iosonofabio/fabiTEM/pcb/3D/SW_SKHLLC.step

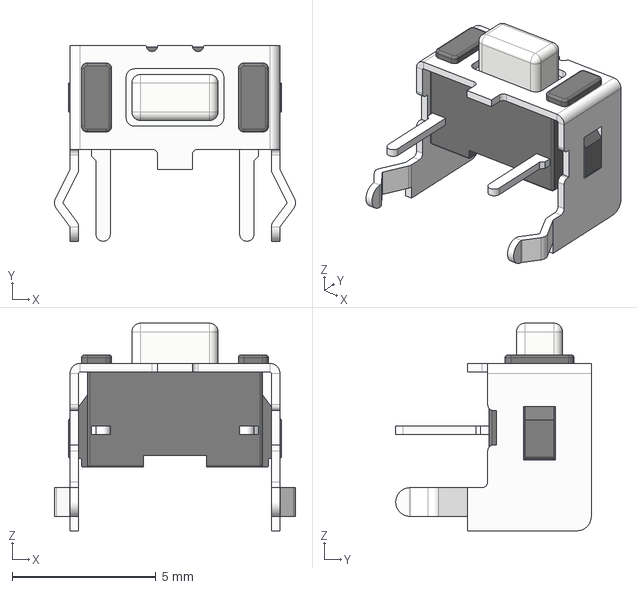
[picture p17: CAD file, 2024-05-21]
pcb/3D/SW_SKHLLC.step
8.38 x 6.80 x 7.22 mm
