iosonofabio/fabiTEM/pcb/3D/D_SOD-123.step

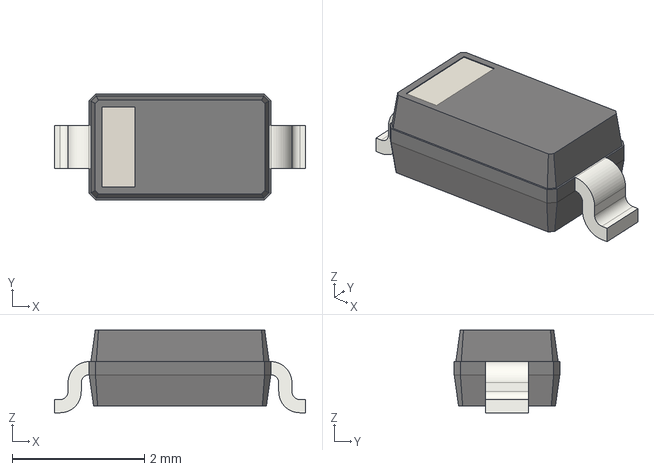
[picture p18: CAD file, 2024-05-21]
pcb/3D/D_SOD-123.step
3.80 x 1.60 x 1.25 mm
