iosonofabio/fabiTEM/pcb/3D/Kailh_socket_PG1350_optional.STEP

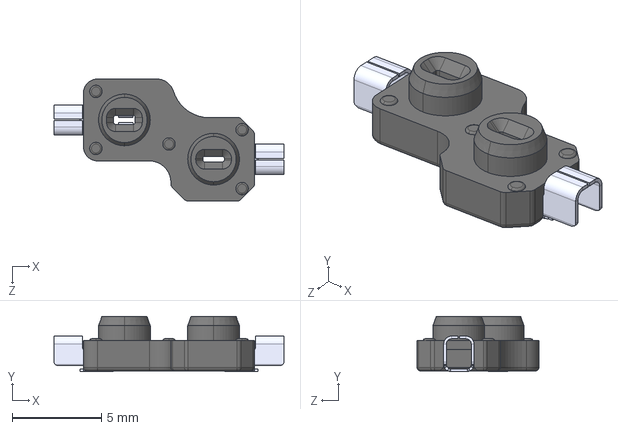
[picture p19: CAD file, 2024-05-21]
pcb/3D/Kailh_socket_PG1350_optional.STEP
12.9 x 3.09 x 6.85 mm
pin x 2
socket
