iosonofabio/fabiTEM/pcb/3D/Kailh_switch_PG1350_optional.step

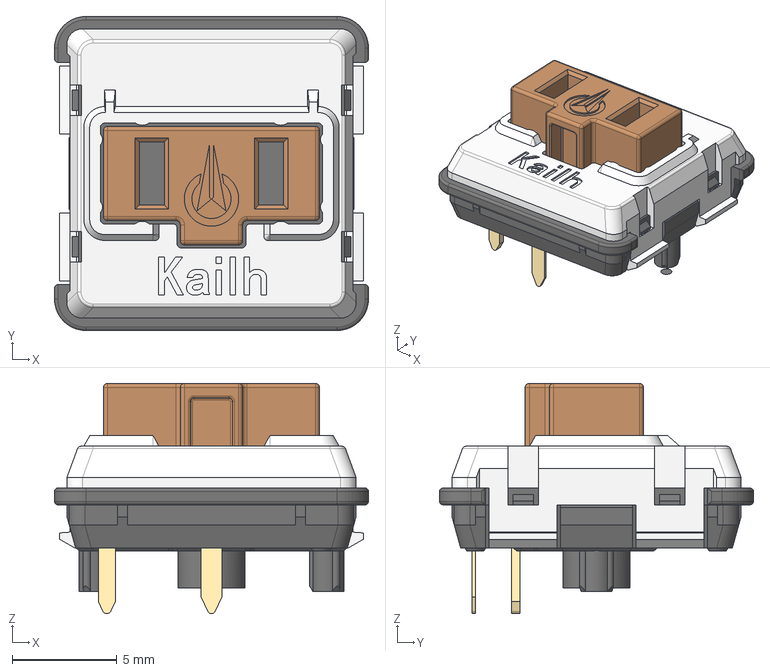
[picture p20: CAD file, 2024-05-21]
pcb/3D/Kailh_switch_PG1350_optional.step
15.0 x 15.0 x 11.0 mm
