iosonofabio/fabiTEM/pcb/3D/MSK12C02.STEP

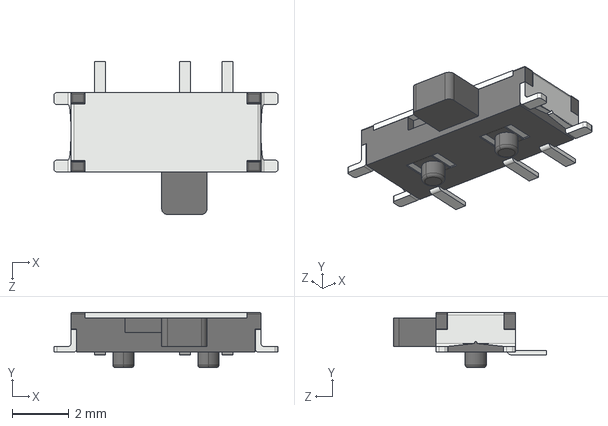
[picture p21: CAD file, 2024-05-21]
pcb/3D/MSK12C02.STEP
7.90 x 1.95 x 5.39 mm
