iosonofabio/fabiTEM/pcb/fabiTEM.kicad_sch

## KiCad design pcb/fabiTEM.kicad_sch (2025-03-23)

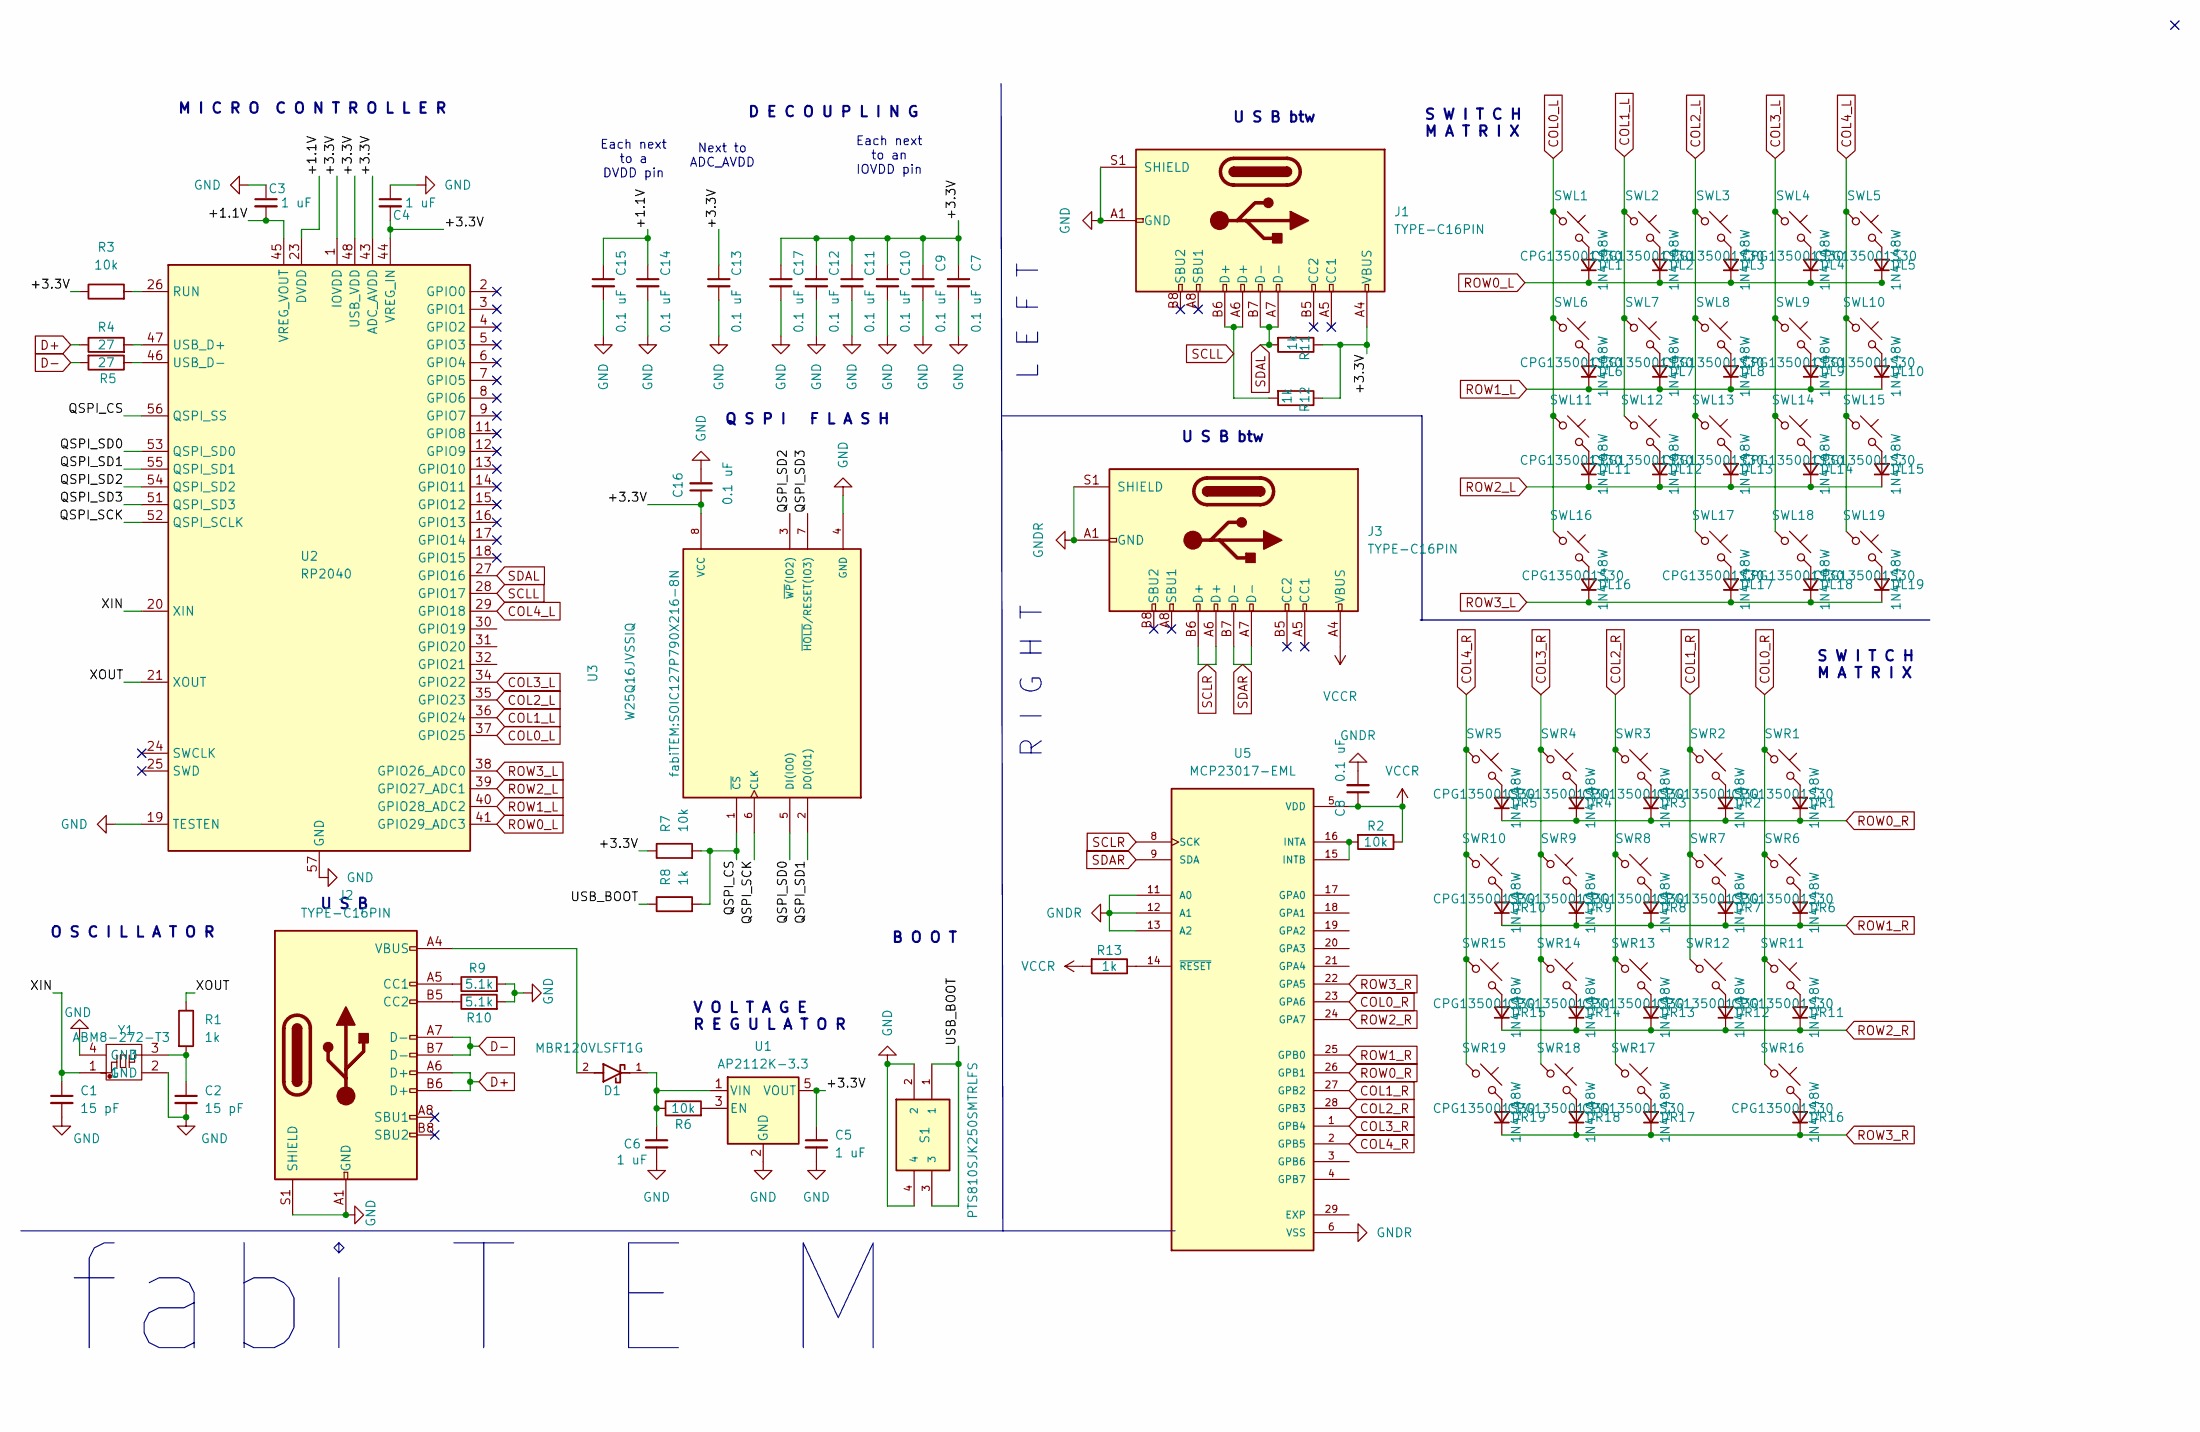
[picture p23: schematic fabiTEM.kicad_sch]

Parts:
C1, C2: 15 pF; C_0201_0603Metric
C3, C4, C5, C6: 1 uF; C_0201_0603Metric
C7, C8, C9, C10, C11, C12, C13, C14, C15, C16, C17: 0.1 uF; C_0201_0603Metric
D1: MBR120VLSFT1G; DIOM3616X98N; PARTREV 5/10/2013
DL1, DL2, DL3, DL4, DL5, DL6, DL7, DL8, DL9, DL10, DL11, DL12, DL13, DL14, DL15, DL16, DL17, DL18, DL19: 1N4148W; Diode_SOD123
DR1, DR2, DR3, DR4, DR5, DR6, DR7, DR8, DR9, DR10, DR11, DR12, DR13, DR14, DR15, DR16, DR17, DR18, DR19: 1N4148W; Diode_SOD123
J1, J2, J3: TYPE-C16PIN; USB_C_Receptacle_GCT_USB4105-xx-A_16P_MidMnt_Horizontal
R1, R8, R11, R12, R13: 1k; R_0201_0603Metric
R2, R3, R6, R7: 10k; R_0201_0603Metric
R4, R5: 27; R_0201_0603Metric
R9, R10: 5.1k; R_0201_0603Metric
S1: PTS810SJK250SMTRLFS; PTS810SJG250SMTRLFS; MANUFACTURER_PART_NUMBER PTS810SJK250SMTRLFS
SWL1, SWL2, SWL3, SWL4, SWL5, SWL6, SWL7, SWL8, SWL9, SWL10, SWL11, SWL12, SWL13, SWL14, SWL15, SWL16, SWL17, SWL18, SWL19: CPG135001S30; Kailh_socket_PG1350_reverse
SWR1, SWR2, SWR3, SWR4, SWR5, SWR6, SWR7, SWR8, SWR9, SWR10, SWR11, SWR12, SWR13, SWR14, SWR15, SWR16, SWR17, SWR18, SWR19: CPG135001S30; Kailh_socket_PG1350_reverse
U1: AP2112K-3.3; SOT-23-5
U2: RP2040; QFN-56-1EP_7x7mm_P0.4mm_EP3.2x3.2mm
U3: W25Q16JVSSIQ; SOIC127P790X216-8N
U5: MCP23017-EML; QFN65P600X600X100-29N; PARTREV C
Y1: ABM8-272-T3

Connections:
+1.1V: C3.2, C14.1, C15.1, U2.23 (DVDD), U2.45 (VREG_VOUT), U2.50 (DVDD)
+3.3V: C4.2, C5.1, C7.1, C9.1, C10.1, C11.1, C12.1, C13.1, C16.1, C17.1, J1.A4 (VBUS), J1.A9 (VBUS), J1.B4 (VBUS), J1.B9 (VBUS), R3.1, R7.1, R11.1, R12.1, U1.5 (VOUT), U2.1 (IOVDD), U2.10 (IOVDD), U2.22 (IOVDD), U2.33 (IOVDD), U2.42 (IOVDD), U2.43 (ADC_AVDD), U2.44 (VREG_IN), U2.48 (USB_VDD), U2.49 (IOVDD), U3.8 (VCC)
COL0_L: SWL1.1, SWL6.1, SWL11.1, SWL16.1, U2.37 (GPIO25)
COL0_R: SWR1.1, SWR6.1, SWR11.1, SWR16.1, U5.23 (GPA6)
COL1_L: SWL2.1, SWL7.1, SWL12.1, U2.36 (GPIO24)
COL1_R: SWR2.1, SWR7.1, SWR12.1, U5.27 (GPB2)
COL2_L: SWL3.1, SWL8.1, SWL13.1, SWL17.1, U2.35 (GPIO23)
COL2_R: SWR3.1, SWR8.1, SWR13.1, SWR17.1, U5.28 (GPB3)
COL3_L: SWL4.1, SWL9.1, SWL14.1, SWL18.1, U2.34 (GPIO22)
COL3_R: SWR4.1, SWR9.1, SWR14.1, SWR18.1, U5.1 (GPB4)
COL4_L: SWL5.1, SWL10.1, SWL15.1, SWL19.1, U2.29 (GPIO18)
COL4_R: SWR5.1, SWR10.1, SWR15.1, SWR19.1, U5.2 (GPB5)
D+: J2.A6 (D+), J2.B6 (D+), R4.1
D-: J2.A7 (D-), J2.B7 (D-), R5.2
GND: C1.2, C2.2, C3.1, C4.1, C5.2, C6.2, C7.2, C9.2, C10.2, C11.2, C12.2, C13.2, C14.2, C15.2, C16.2, C17.2, J1.A1 (GND), J1.A12 (GND), J1.B1 (GND), J1.B12 (GND), J1.S1 (SHIELD), J2.A1 (GND), J2.A12 (GND), J2.B1 (GND), J2.B12 (GND), J2.S1 (SHIELD), R9.2, R10.2, S1.2, S1.4, U1.2 (GND), U2.19 (TESTEN), U2.57 (GND), U3.4 (GND), Y1.2 (GND), Y1.4 (GND)
GNDR: C8.2, J3.A1 (GND), J3.A12 (GND), J3.B1 (GND), J3.B12 (GND), J3.S1 (SHIELD), U5.6 (VSS), U5.11 (A0), U5.12 (A1), U5.13 (A2)
unnamed: C2.1, R1.2, Y1.3
unnamed: C6.1, D1.1, R6.1, U1.1 (VIN)
unnamed: D1.2, J2.A4 (VBUS), J2.A9 (VBUS), J2.B4 (VBUS), J2.B9 (VBUS)
unnamed: DL1.2 (A), SWL1.2
unnamed: DL2.2 (A), SWL2.2
unnamed: DL3.2 (A), SWL3.2
unnamed: DL4.2 (A), SWL4.2
unnamed: DL5.2 (A), SWL5.2
unnamed: DL6.2 (A), SWL6.2
unnamed: DL7.2 (A), SWL7.2
unnamed: DL8.2 (A), SWL8.2
unnamed: DL9.2 (A), SWL9.2
unnamed: DL10.2 (A), SWL10.2
unnamed: DL11.2 (A), SWL11.2
unnamed: DL12.2 (A), SWL12.2
unnamed: DL13.2 (A), SWL13.2
unnamed: DL14.2 (A), SWL14.2
unnamed: DL15.2 (A), SWL15.2
unnamed: DL16.2 (A), SWL16.2
unnamed: DL17.2 (A), SWL17.2
unnamed: DL18.2 (A), SWL18.2
unnamed: DL19.2 (A), SWL19.2
unnamed: DR1.2 (A), SWR1.2
unnamed: DR2.2 (A), SWR2.2
unnamed: DR3.2 (A), SWR3.2
unnamed: DR4.2 (A), SWR4.2
unnamed: DR5.2 (A), SWR5.2
unnamed: DR6.2 (A), SWR6.2
unnamed: DR7.2 (A), SWR7.2
unnamed: DR8.2 (A), SWR8.2
unnamed: DR9.2 (A), SWR9.2
unnamed: DR10.2 (A), SWR10.2
unnamed: DR11.2 (A), SWR11.2
unnamed: DR12.2 (A), SWR12.2
unnamed: DR13.2 (A), SWR13.2
unnamed: DR14.2 (A), SWR14.2
unnamed: DR15.2 (A), SWR15.2
unnamed: DR16.2 (A), SWR16.2
unnamed: DR17.2 (A), SWR17.2
unnamed: DR18.2 (A), SWR18.2
unnamed: DR19.2 (A), SWR19.2
unnamed: J2.A5 (CC1), R9.1
unnamed: J2.B5 (CC2), R10.1
unnamed: R2.2, U5.15 (INTB), U5.16 (INTA)
unnamed: R3.2, U2.26 (RUN)
unnamed: R4.2, U2.47 (USB_D+)
unnamed: R5.1, U2.46 (USB_D-)
unnamed: R6.2, U1.3 (EN)
unnamed: R13.1, U5.14 (~RESET)
QSPI_CS: R7.2, R8.2, U2.56 (QSPI_SS), U3.1 (~CS)
QSPI_SCK: U2.52 (QSPI_SCLK), U3.6 (CLK)
QSPI_SD0: U2.53 (QSPI_SD0), U3.5 (DI(IO0))
QSPI_SD1: U2.55 (QSPI_SD1), U3.2 (DO(IO1))
QSPI_SD2: U2.54 (QSPI_SD2), U3.3 (~WP(IO2))
QSPI_SD3: U2.51 (QSPI_SD3), U3.7 (~HOLD/RESET(IO3))
ROW0_L: DL1.1 (K), DL2.1 (K), DL3.1 (K), DL4.1 (K), DL5.1 (K), U2.41 (GPIO29_ADC3)
ROW0_R: DR1.1 (K), DR2.1 (K), DR3.1 (K), DR4.1 (K), DR5.1 (K), U5.26 (GPB1)
ROW1_L: DL6.1 (K), DL7.1 (K), DL8.1 (K), DL9.1 (K), DL10.1 (K), U2.40 (GPIO28_ADC2)
ROW1_R: DR6.1 (K), DR7.1 (K), DR8.1 (K), DR9.1 (K), DR10.1 (K), U5.25 (GPB0)
ROW2_L: DL11.1 (K), DL12.1 (K), DL13.1 (K), DL14.1 (K), DL15.1 (K), U2.39 (GPIO27_ADC1)
ROW2_R: DR11.1 (K), DR12.1 (K), DR13.1 (K), DR14.1 (K), DR15.1 (K), U5.24 (GPA7)
ROW3_L: DL16.1 (K), DL17.1 (K), DL18.1 (K), DL19.1 (K), U2.38 (GPIO26_ADC0)
ROW3_R: DR16.1 (K), DR17.1 (K), DR18.1 (K), DR19.1 (K), U5.22 (GPA5)
SCLL: J1.A6 (D+), J1.B6 (D+), R12.2, U2.28 (GPIO17)
SCLR: J3.A6 (D+), J3.B6 (D+), U5.8 (SCK)
SDAL: J1.A7 (D-), J1.B7 (D-), R11.2, U2.27 (GPIO16)
SDAR: J3.A7 (D-), J3.B7 (D-), U5.9 (SDA)
USB_BOOT: R8.1, S1.1, S1.3
VCCR: C8.1, J3.A4 (VBUS), J3.A9 (VBUS), J3.B4 (VBUS), J3.B9 (VBUS), R2.1, R13.2, U5.5 (VDD)
XIN: C1.1, U2.20 (XIN), Y1.1
XOUT: R1.1, U2.21 (XOUT)

Notes on the sheet:
Next to ADC_AVDD
Each next to an IOVDD pin
U S B btw
Q S P I F L A S H
S W I T C H M A T R I X
B O O T
fabi T E M
V O L T A G E R E G U L A T O R
U S B
Each next to a DVDD pin
O S C I L L A T O R
D E C O U P L I N G
R I G H T
L E F T
M I C R O C O N T R O L L E R
